keyquesttech/Rtv6/Rtv6-2/Package/Card_assets/9793.jpg

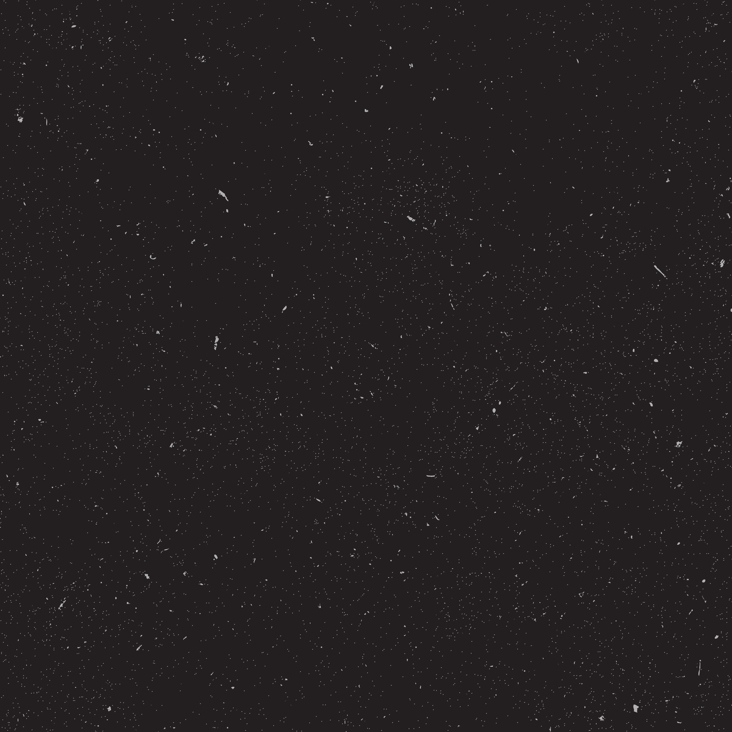
Rtv6-2/Package/Card_assets/9793.jpg
